karolis1115/Matronix/Pictures/20221025_215015.jpg

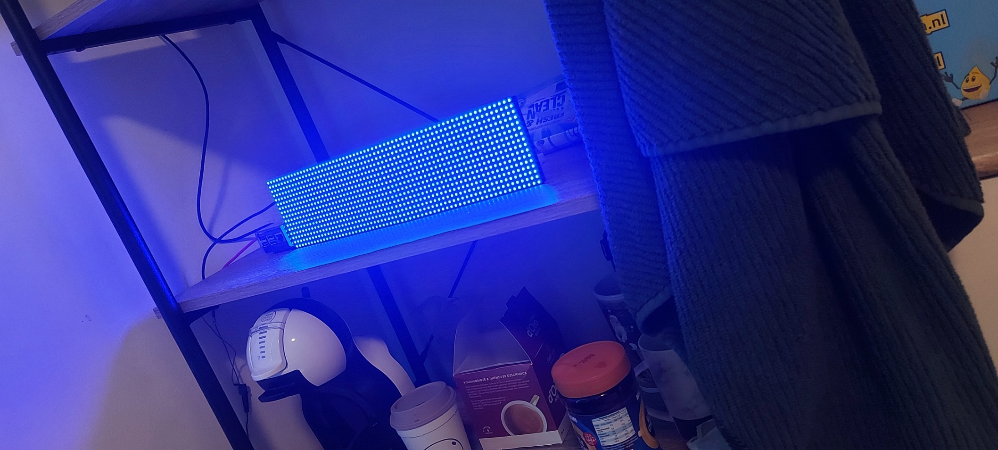
Pictures/20221025_215015.jpg
