karolis1115/Matronix/Pictures/20221025_220137.jpg

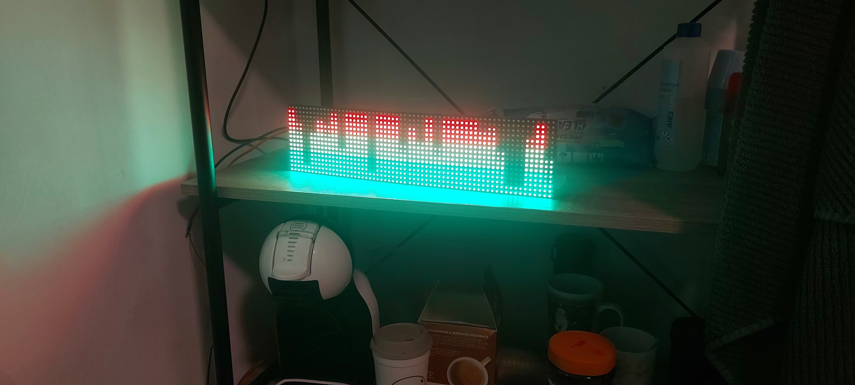
Pictures/20221025_220137.jpg
