karolis1115/Matronix/Pictures/20221025_220200.jpg

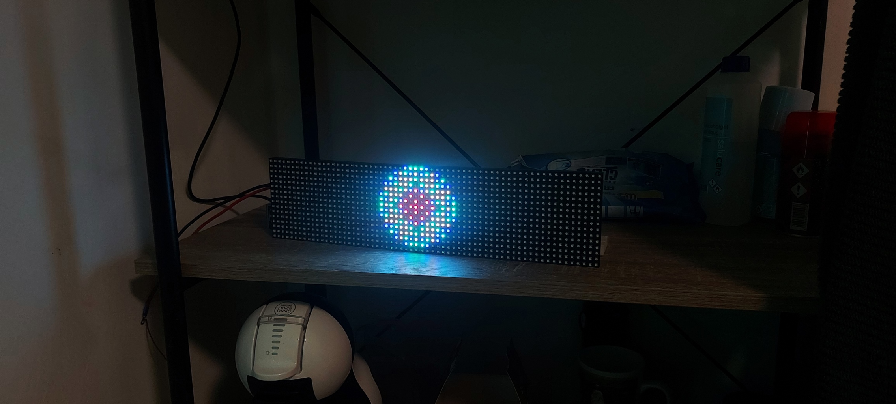
Pictures/20221025_220200.jpg
