karolis1115/Matronix/CAD/PCB assembly with all edge connectors V2/Dimmension_test.3mf

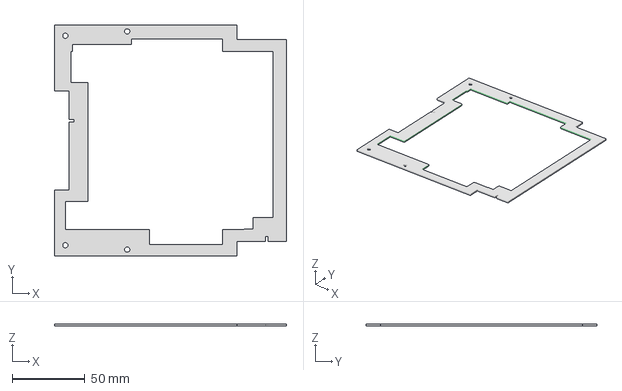
[picture p37: CAD file, 2023-01-07]
CAD/PCB assembly with all edge connectors V2/Dimmension_test.3mf
159.5 x 159.0 x 1.52 mm
