karolis1115/Matronix/CAD/PCB outline with 3 edge connectors and Raspberry pi outline/2x20 Stacking Header.step.SLDPRT

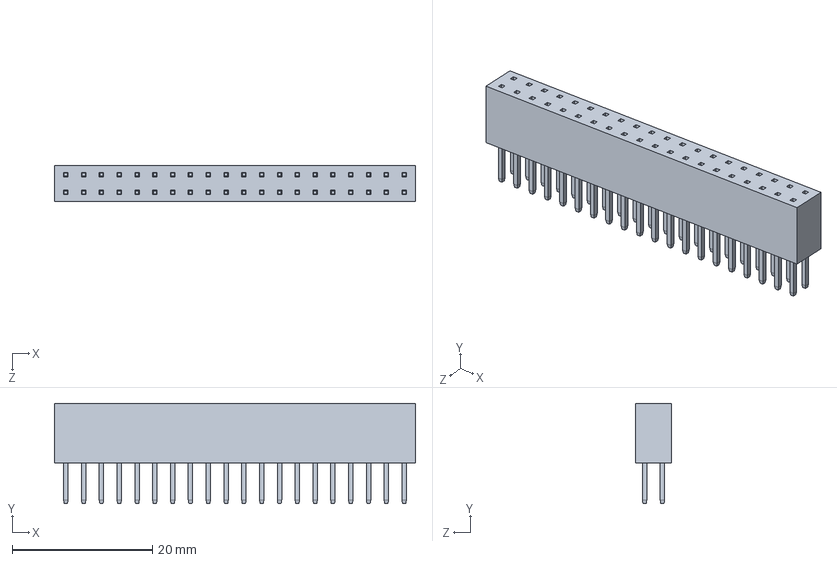
[picture p38: CAD file, 2023-01-07]
CAD/PCB outline with 3 edge connectors and Raspberry pi outline/2x20 Stacking Header.step.SLDPRT
51.5 x 14.3 x 5.08 mm
