karolis1115/Matronix/CAD/PCB outline with 3 edge connectors and Raspberry pi outline/raspberry-pi-4-model-b-1.snapshot.3/Microphone Plug, RPi4ModelB.SLDPRT

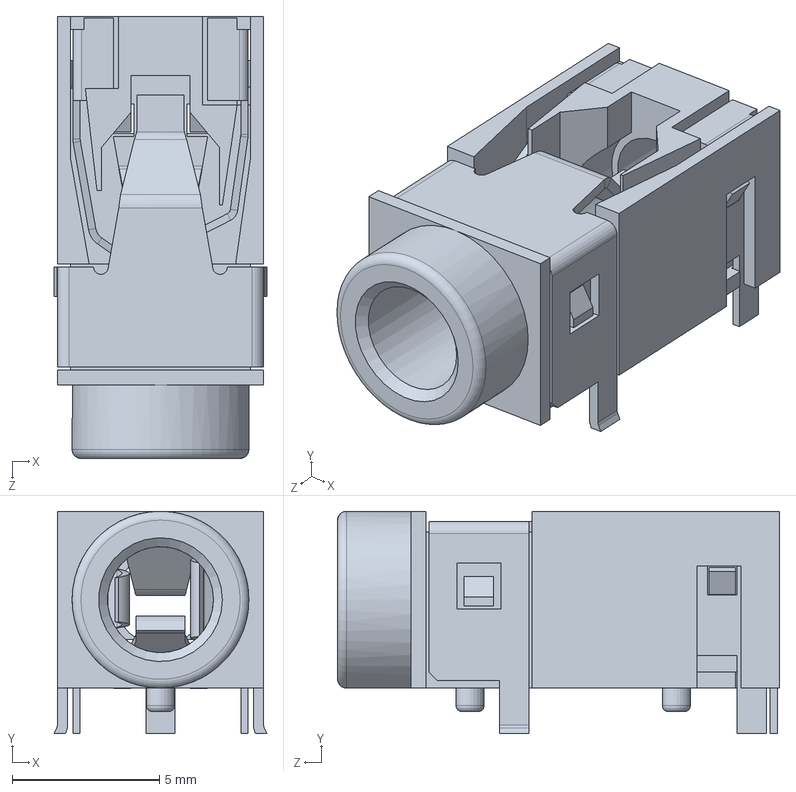
[picture p39: CAD file, 2023-01-07]
CAD/PCB outline with 3 edge connectors and Raspberry pi outline/raspberry-pi-4-model-b-1.snapshot.3/Microphone Plug, RPi4ModelB.SLDPRT
7.23 x 7.55 x 15.0 mm
