karolis1115/Matronix/3D models/LED DISPLAY 32x16 Adafruit.SLDPRT

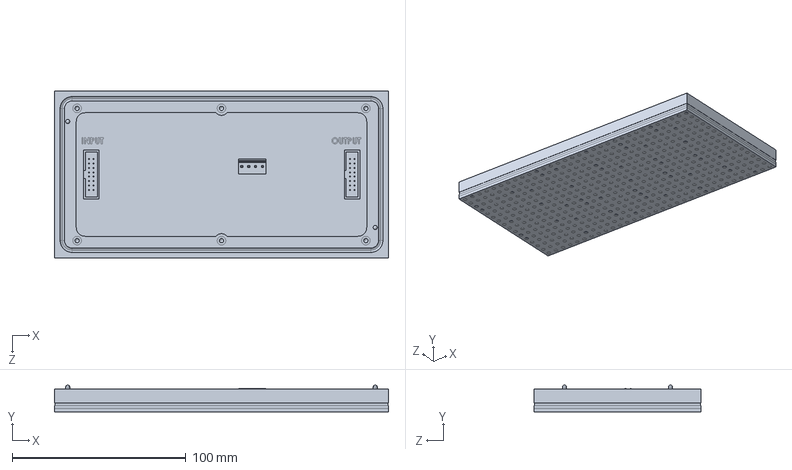
[picture p40: CAD file, 2023-01-07]
3D models/LED DISPLAY 32x16 Adafruit.SLDPRT
192.0 x 15.5 x 96.0 mm
