karolis1115/Matronix/CAD/DIsplay Module PCB.STEP

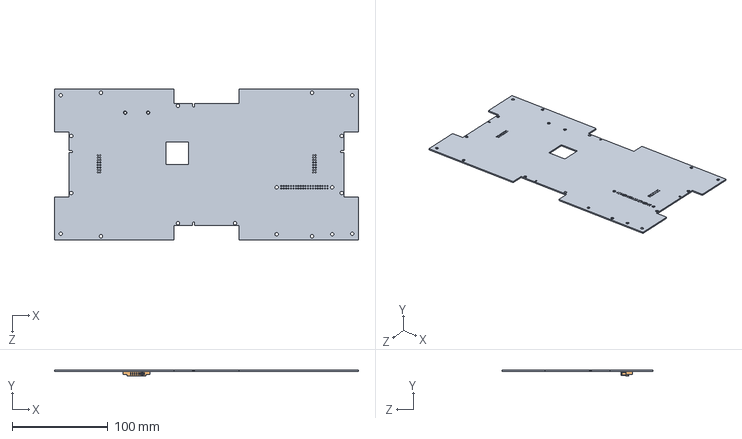
[picture p42: CAD file, 2023-01-21]
CAD/DIsplay Module PCB.STEP
317.5 x 6.37 x 157.5 mm
PCB
