karolis1115/Matronix/CAD/LED Matrix Display Redesign/DIsplay Module PCB.3MF

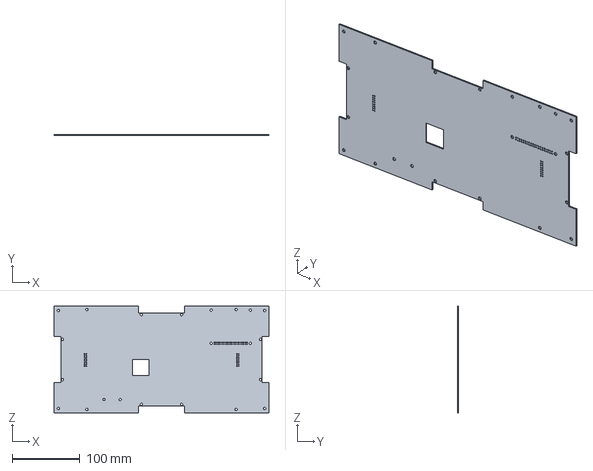
[picture p43: CAD file, 2023-01-07]
CAD/LED Matrix Display Redesign/DIsplay Module PCB.3MF
317.5 x 1.57 x 157.5 mm
