karolis1115/Matronix/CAD/LED Matrix Display Redesign/raspberry-pi-4-model-b-1.snapshot.3/Female Micro HDMI Connector, RPi4ModelB.SLDPRT

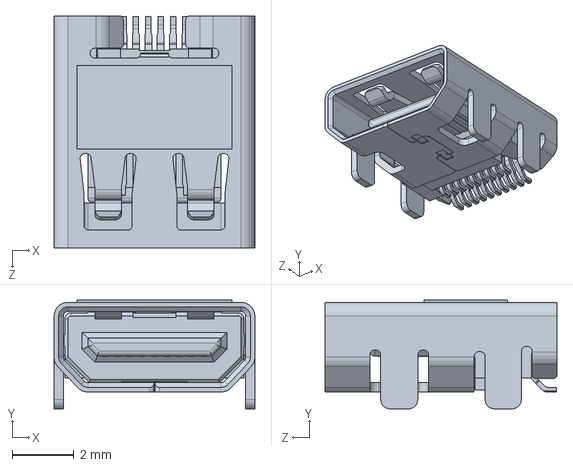
[picture p44: CAD file, 2023-01-07]
CAD/LED Matrix Display Redesign/raspberry-pi-4-model-b-1.snapshot.3/Female Micro HDMI Connector, RPi4ModelB.SLDPRT
6.50 x 3.52 x 7.50 mm
