karolis1115/Matronix/CAD/PCB assembly w Edge connectors/PCB asembly w Edge Connectors V2.3mf

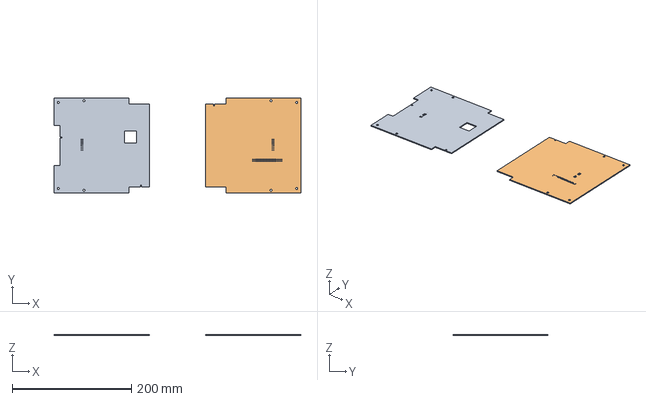
[picture p45: CAD file, 2023-01-07]
CAD/PCB assembly w Edge connectors/PCB asembly w Edge Connectors V2.3mf
413.6 x 159.0 x 1.58 mm
