karolis1115/Matronix/CAD/PCB assembly with all edge connectors V2/Box Header 8x2 16 pin.SLDPRT

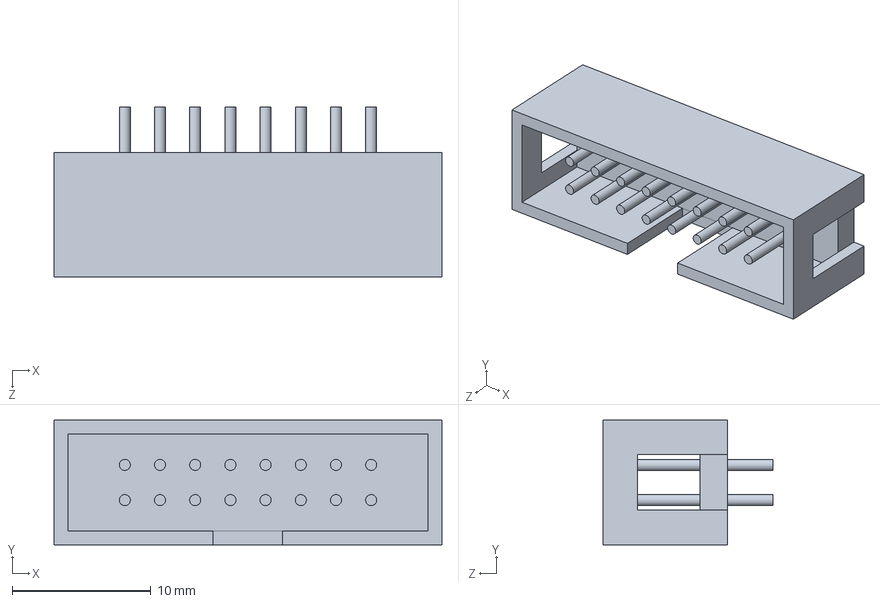
[picture p46: CAD file, 2023-01-07]
CAD/PCB assembly with all edge connectors V2/Box Header 8x2 16 pin.SLDPRT
28.0 x 9.00 x 12.3 mm
