karolis1115/Matronix/CAD/PCB assembly/PCB asembly split.3mf

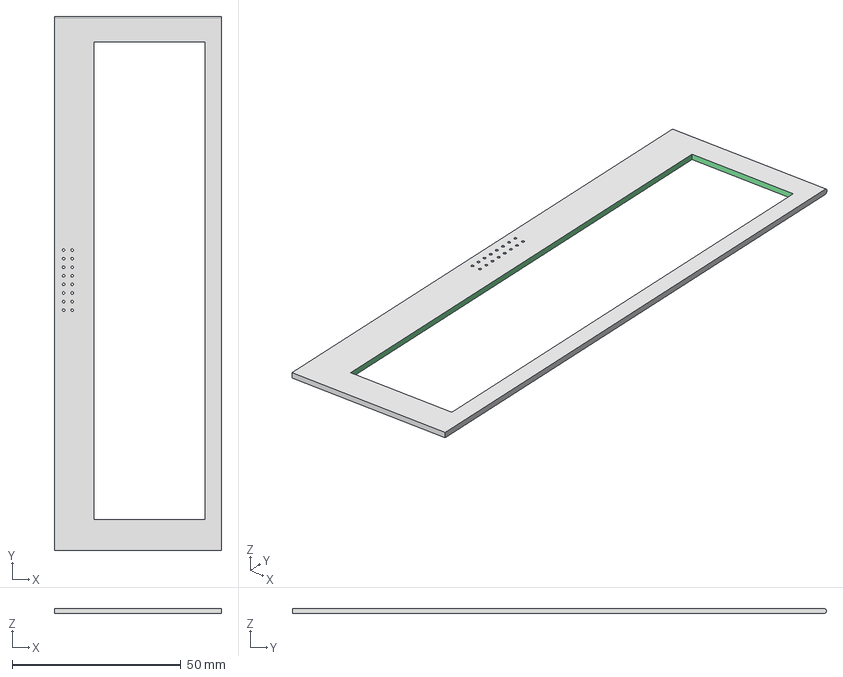
[picture p47: CAD file, 2023-01-07]
CAD/PCB assembly/PCB asembly split.3mf
49.5 x 158.0 x 1.57 mm
