karolis1115/Matronix/CAD/PCB outline with 3 edge connectors and Raspberry pi outline/PCB asembly w Edge Connectors hollowed.3mf

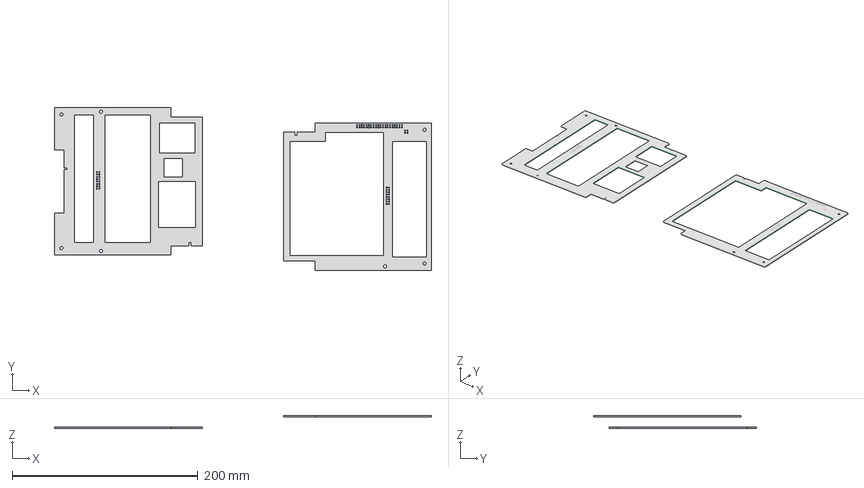
[picture p48: CAD file, 2023-01-07]
CAD/PCB outline with 3 edge connectors and Raspberry pi outline/PCB asembly w Edge Connectors hollowed.3mf
406.1 x 175.5 x 14.0 mm
