karolis1115/Matronix/CAD/PCB outline with 3 edge connectors and Raspberry pi outline/raspberry-pi-4-model-b-1.snapshot.3/MxL7704 Universal PMIC, RPi4ModelB.SLDPRT

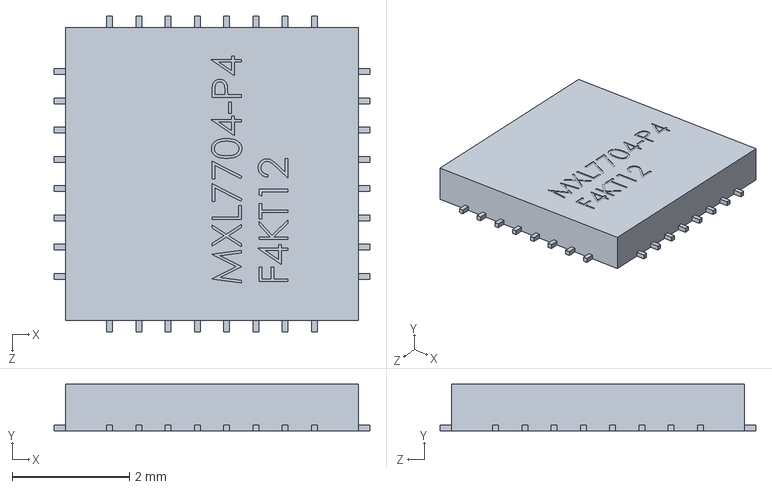
[picture p49: CAD file, 2023-01-07]
CAD/PCB outline with 3 edge connectors and Raspberry pi outline/raspberry-pi-4-model-b-1.snapshot.3/MxL7704 Universal PMIC, RPi4ModelB.SLDPRT
5.40 x 0.8 x 5.40 mm
