karolis1115/Matronix/CAD/LED Matrix Display Redesign/raspberry-pi-4-model-b-1.snapshot.3/Broadcom BCM54213PE Gigabit Ethernet Transceiver, RPi4ModelB.SLDPRT

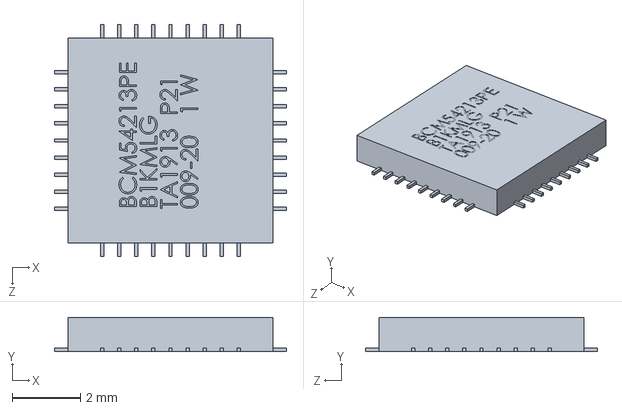
[picture p50: CAD file, 2023-01-07]
CAD/LED Matrix Display Redesign/raspberry-pi-4-model-b-1.snapshot.3/Broadcom BCM54213PE Gigabit Ethernet Transceiver, RPi4ModelB.SLDPRT
6.80 x 1.00 x 6.80 mm
