karolis1115/Matronix/CAD/PCB assembly with all edge connectors V2/PCB asembly w Edge Connectors.DXF

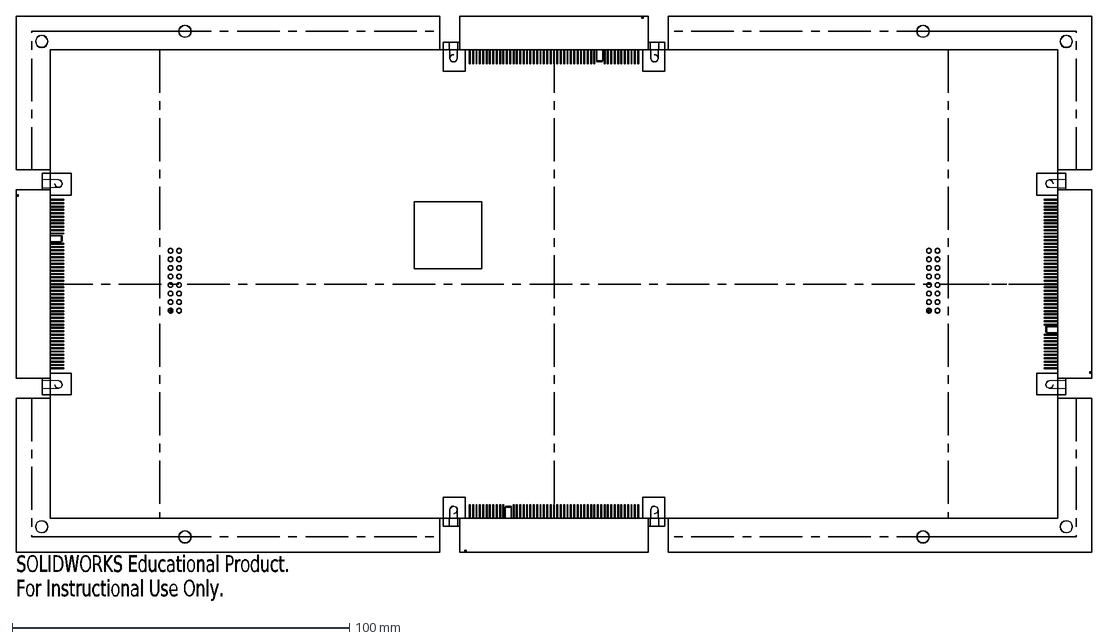
[picture p51: CAD file, 2023-01-07]
CAD/PCB assembly with all edge connectors V2/PCB asembly w Edge Connectors.DXF
SOLIDWORKS Educational Product.
For Instructional Use Only.
