karolis1115/Matronix/CAD/PCB assembly/PCB asemblyV2 split.stl

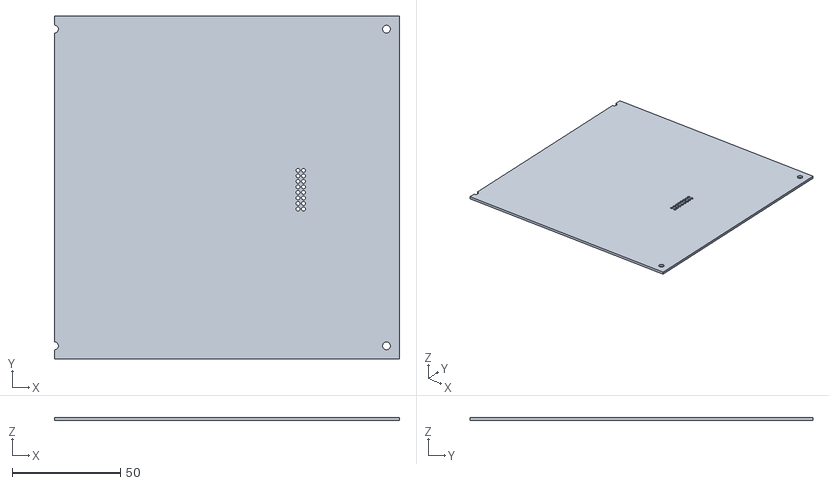
[picture p52: CAD file, 2023-01-07]
CAD/PCB assembly/PCB asemblyV2 split.stl
159.0 x 158.0 x 1.57
