karolis1115/Matronix/CAD/PCB outline with 3 edge connectors and Raspberry pi outline/PCB asembly w Edge Connectors V2.STL

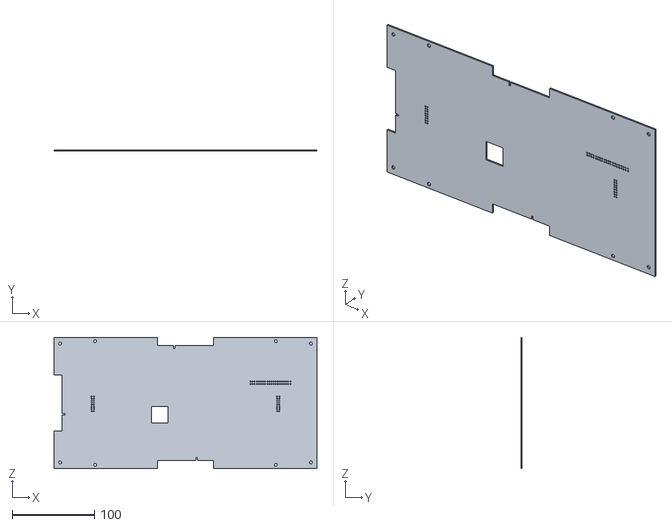
[picture p53: CAD file, 2023-01-07]
CAD/PCB outline with 3 edge connectors and Raspberry pi outline/PCB asembly w Edge Connectors V2.STL
319.0 x 1.57 x 159.0
