karolis1115/Matronix/CAD/PCB outline with 3 edge connectors and Raspberry pi outline/raspberry-pi-4-model-b-1.snapshot.3/2.54 mm DUPONT MALE PIN HEADER, IO, 2X20, RPi4ModelB.SLDPRT

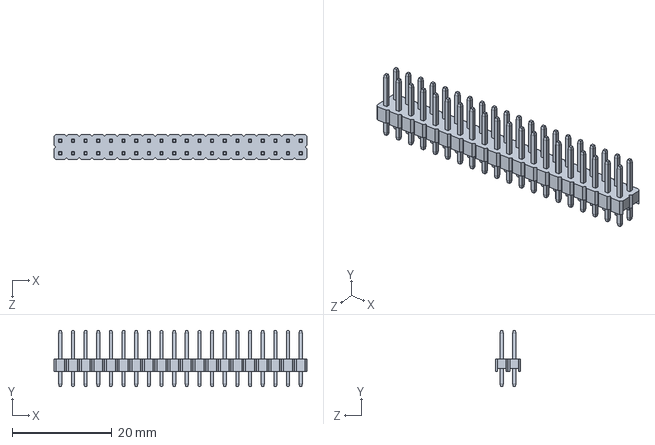
[picture p54: CAD file, 2023-01-07]
CAD/PCB outline with 3 edge connectors and Raspberry pi outline/raspberry-pi-4-model-b-1.snapshot.3/2.54 mm DUPONT MALE PIN HEADER, IO, 2X20, RPi4ModelB.SLDPRT
50.8 x 11.3 x 5.08 mm
