karolis1115/Matronix/CAD/LED Matrix Display Redesign/raspberry-pi-4-model-b-1.snapshot.3/Camera Connector, RPi4ModelB.SLDPRT

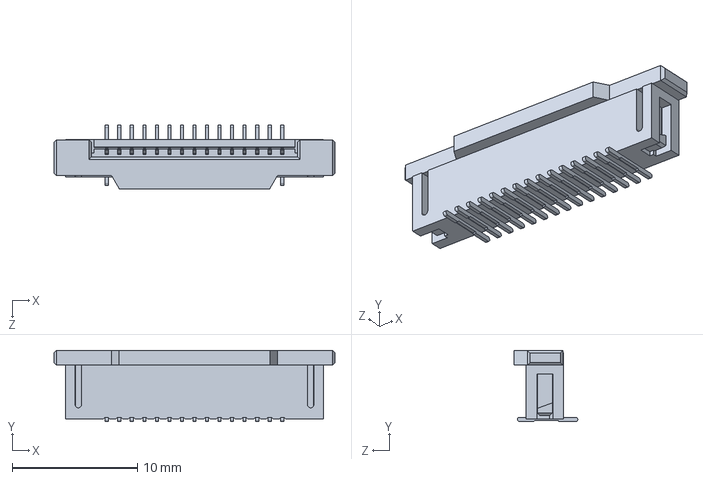
[picture p55: CAD file, 2023-01-07]
CAD/LED Matrix Display Redesign/raspberry-pi-4-model-b-1.snapshot.3/Camera Connector, RPi4ModelB.SLDPRT
22.4 x 5.68 x 5.07 mm
