karolis1115/Matronix/CAD/PCB assembly/PCB asembly V3_Gutted.3mf

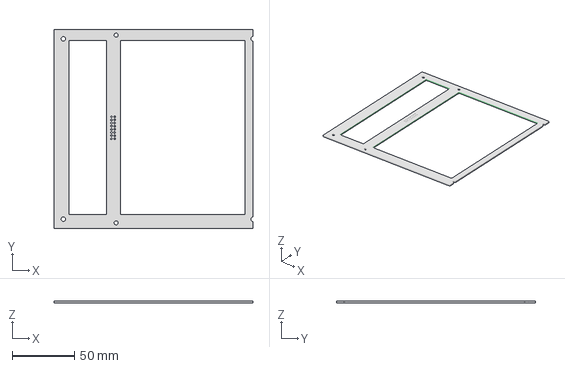
[picture p56: CAD file, 2023-01-07]
CAD/PCB assembly/PCB asembly V3_Gutted.3mf
160.0 x 160.0 x 1.57 mm
