karolis1115/Matronix/3D models/raspberry-pi-4-model-b-1.snapshot.3/2X USB3.0 PORTS, RPi4ModelB.SLDPRT

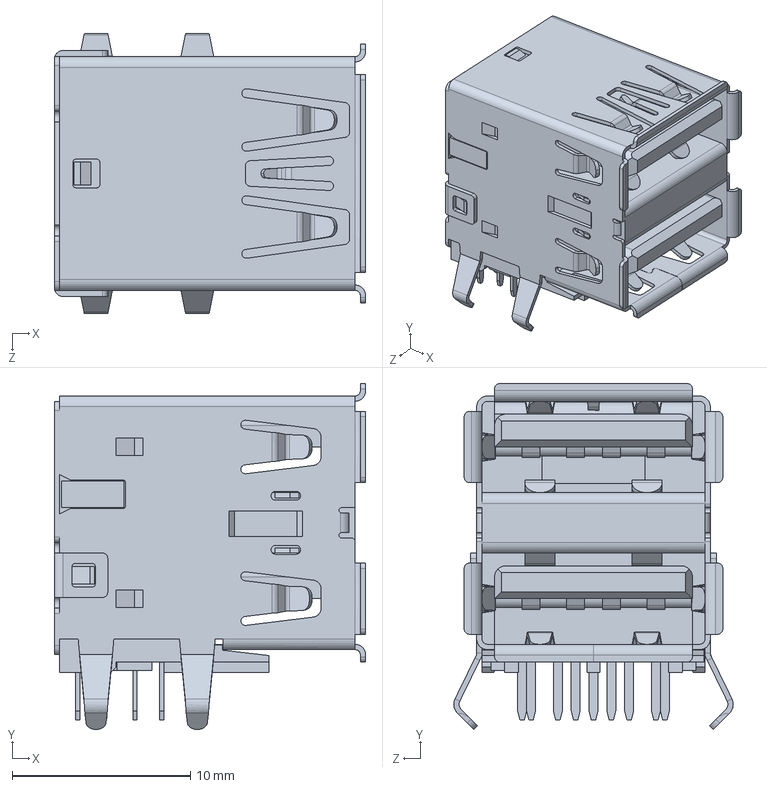
[picture p57: CAD file, 2023-01-07]
3D models/raspberry-pi-4-model-b-1.snapshot.3/2X USB3.0 PORTS, RPi4ModelB.SLDPRT
17.5 x 19.4 x 15.7 mm
