karolis1115/Matronix/CAD/LED Matrix Display Redesign/40 Pin Long Female header.SLDPRT

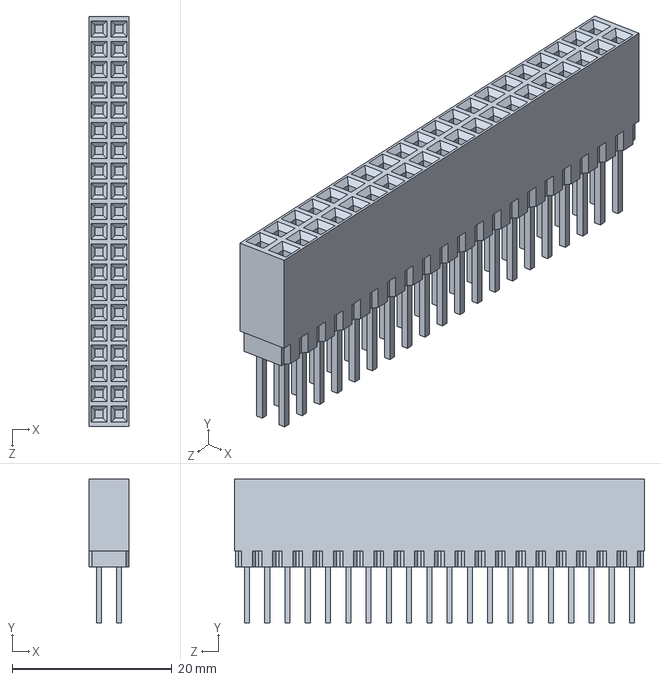
[picture p58: CAD file, 2023-01-07]
CAD/LED Matrix Display Redesign/40 Pin Long Female header.SLDPRT
5.00 x 18.0 x 51.4 mm
