karolis1115/Matronix/CAD/PCB assembly w Edge connectors/PCB asembly Connector allignment.DXF

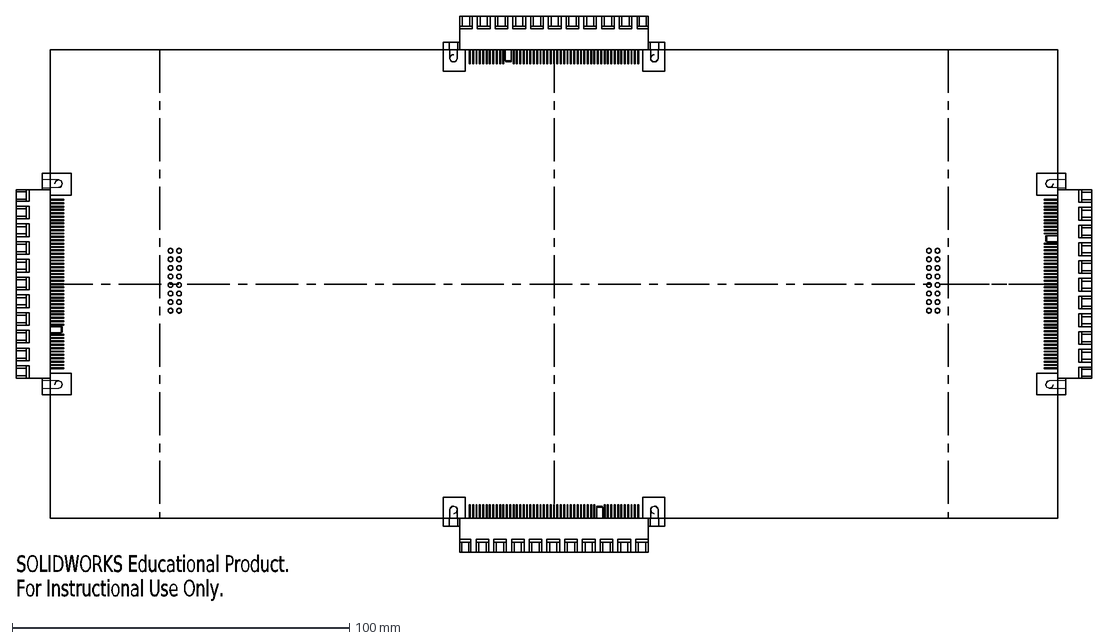
[picture p59: CAD file, 2023-01-07]
CAD/PCB assembly w Edge connectors/PCB asembly Connector allignment.DXF
SOLIDWORKS Educational Product.
For Instructional Use Only.
