karolis1115/Matronix/CAD/PCB assembly/PCB asembly+DimpleHoles_SPlit+Guttedmf.3mf

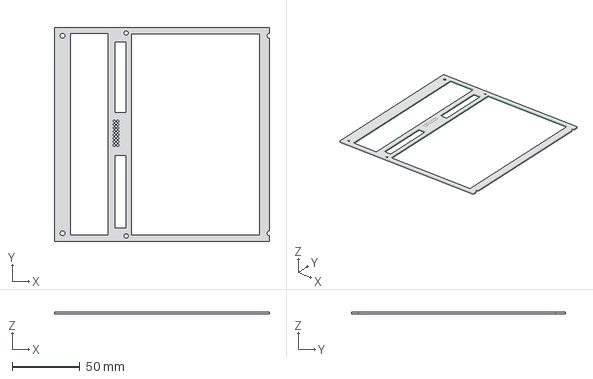
[picture p60: CAD file, 2023-01-07]
CAD/PCB assembly/PCB asembly+DimpleHoles_SPlit+Guttedmf.3mf
159.0 x 158.0 x 1.57 mm
