karolis1115/Matronix/CAD/PCB outline with 3 edge connectors and Raspberry pi outline/female_header_a-bl254-eg-g02d.stp.SLDPRT

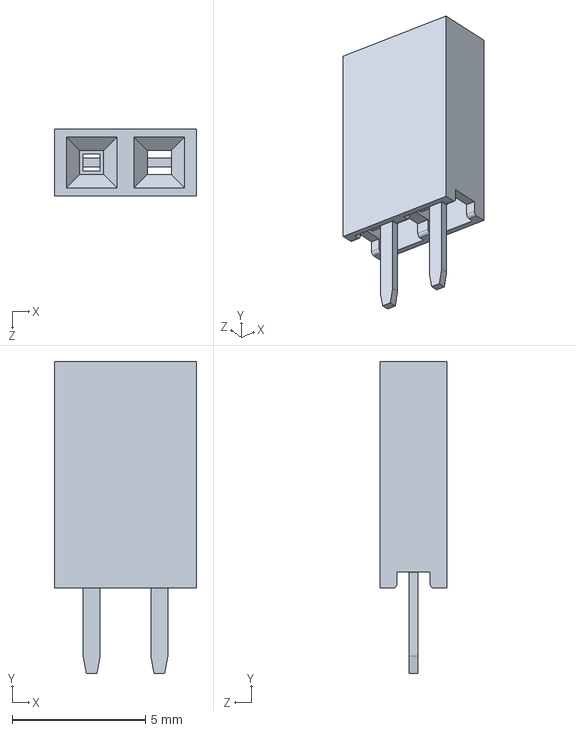
[picture p61: CAD file, 2023-01-07]
CAD/PCB outline with 3 edge connectors and Raspberry pi outline/female_header_a-bl254-eg-g02d.stp.SLDPRT
5.33 x 11.7 x 2.50 mm
