karolis1115/Matronix/CAD/PCB outline with 3 edge connectors and Raspberry pi outline/raspberry-pi-4-model-b-1.snapshot.3/VIA VL805 PCIe USB 3.0 controller, RPi4ModelB.SLDPRT

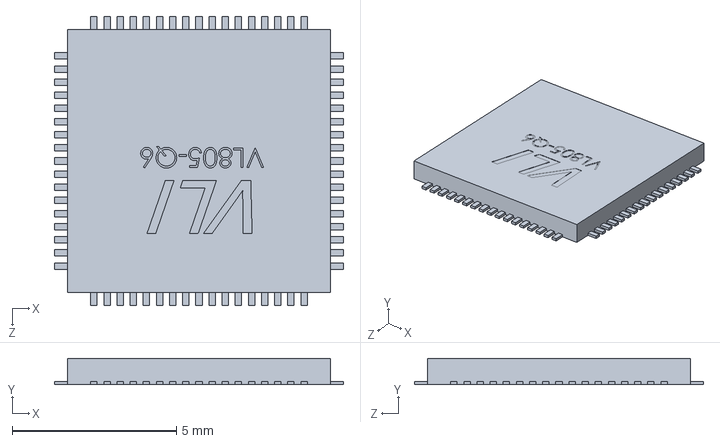
[picture p62: CAD file, 2023-01-07]
CAD/PCB outline with 3 edge connectors and Raspberry pi outline/raspberry-pi-4-model-b-1.snapshot.3/VIA VL805 PCIe USB 3.0 controller, RPi4ModelB.SLDPRT
8.80 x 0.8 x 8.80 mm
