karolis1115/Matronix/3D models/raspberry-pi-4-model-b-1.snapshot.3/Cypress CYW43455 Wireless Module Cover, RPi4ModelB.SLDPRT

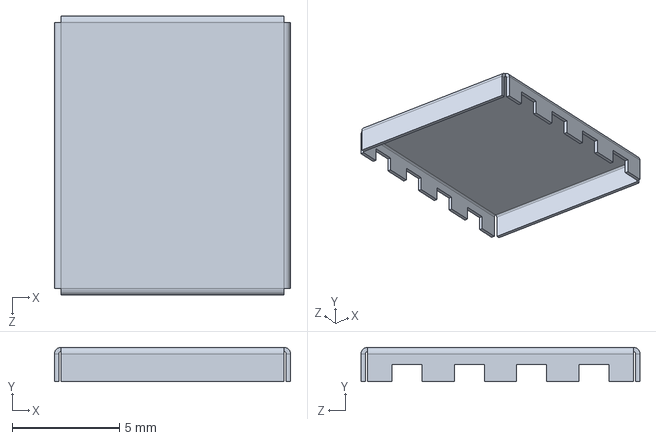
[picture p63: CAD file, 2023-01-07]
3D models/raspberry-pi-4-model-b-1.snapshot.3/Cypress CYW43455 Wireless Module Cover, RPi4ModelB.SLDPRT
11.0 x 1.60 x 13.0 mm
