karolis1115/Matronix/CAD/LED Matrix Display Redesign/DIsplay Module PCB split.3mf

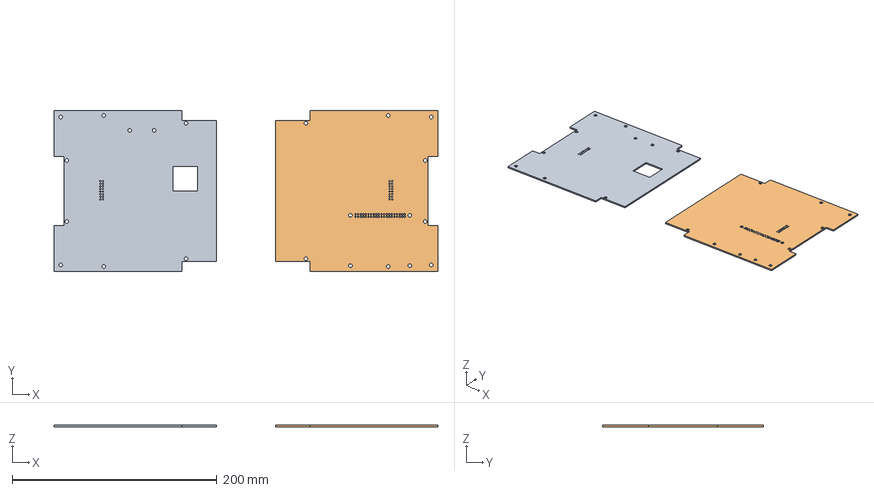
[picture p64: CAD file, 2023-01-07]
CAD/LED Matrix Display Redesign/DIsplay Module PCB split.3mf
375.0 x 157.5 x 1.57 mm
