karolis1115/Matronix/CAD/PCB assembly w Edge connectors/PCB asembly w Edge ConnectorsV3 (fixed edge connector rotation).DXF

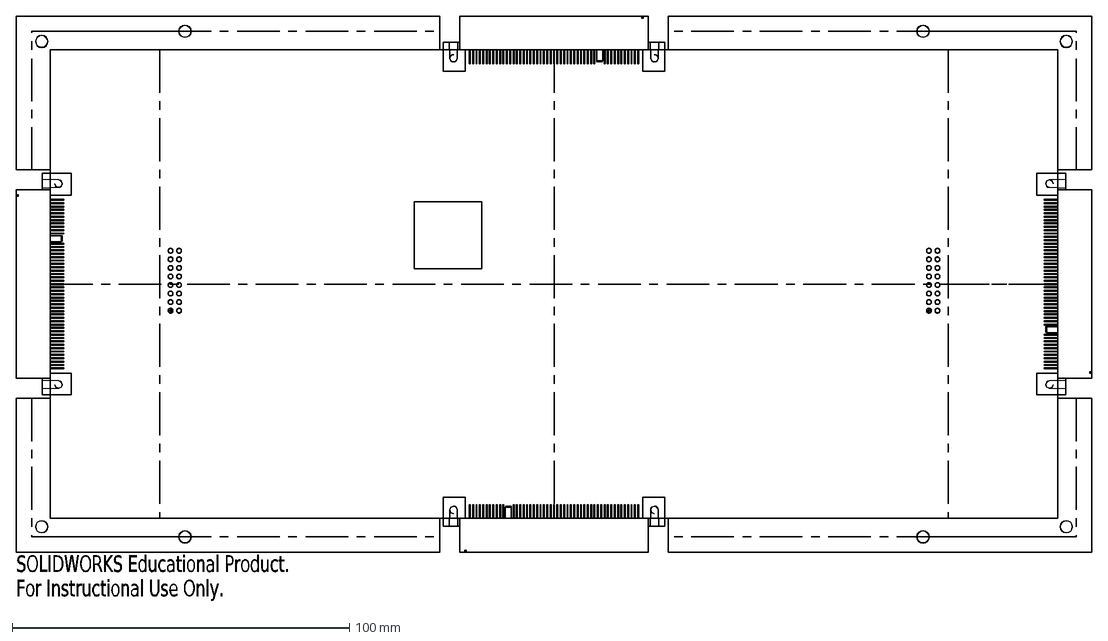
[picture p65: CAD file, 2023-01-07]
CAD/PCB assembly w Edge connectors/PCB asembly w Edge ConnectorsV3 (fixed edge connector rotation).DXF
SOLIDWORKS Educational Product.
For Instructional Use Only.
