karolis1115/Matronix/CAD/LED Matrix Display Redesign/raspberry-pi-4-model-b-1.snapshot.3/PCB, RPi4ModelB.SLDPRT

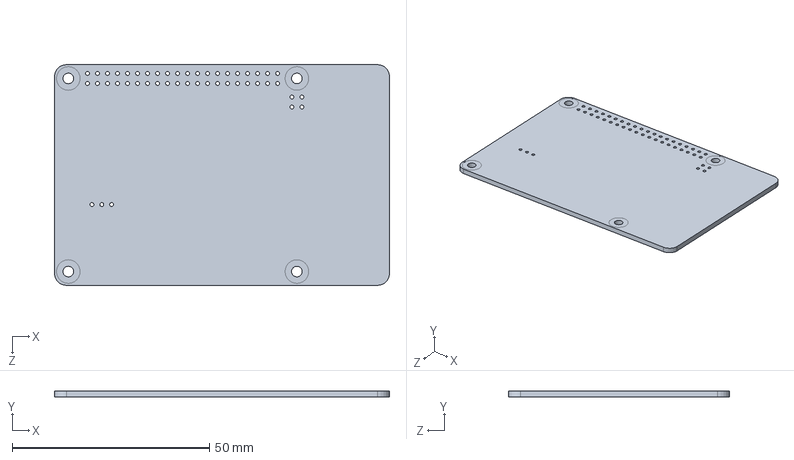
[picture p66: CAD file, 2023-01-07]
CAD/LED Matrix Display Redesign/raspberry-pi-4-model-b-1.snapshot.3/PCB, RPi4ModelB.SLDPRT
85.0 x 1.60 x 56.0 mm
