karolis1115/Matronix/CAD/PCB assembly/PCB asemblyV2 split&hollowed.3mf

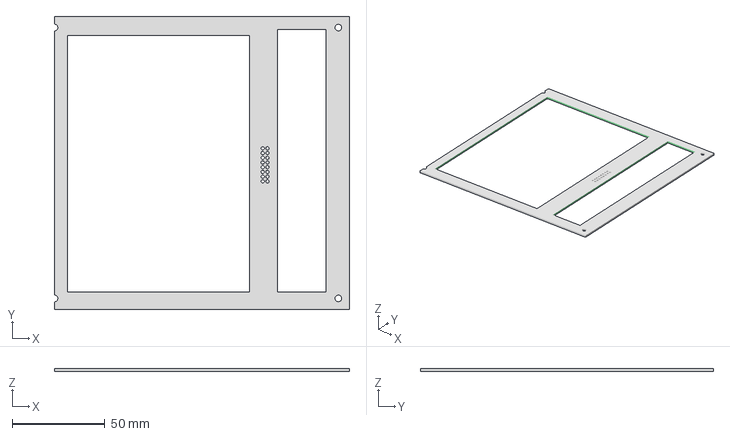
[picture p67: CAD file, 2023-01-07]
CAD/PCB assembly/PCB asemblyV2 split&hollowed.3mf
159.0 x 158.0 x 1.57 mm
