karolis1115/Matronix/CAD/PCB outline with 3 edge connectors and Raspberry pi outline/raspberry-pi-4-model-b-1.snapshot.3/Gigabit Ethernet Port, RPi4ModelB.SLDPRT

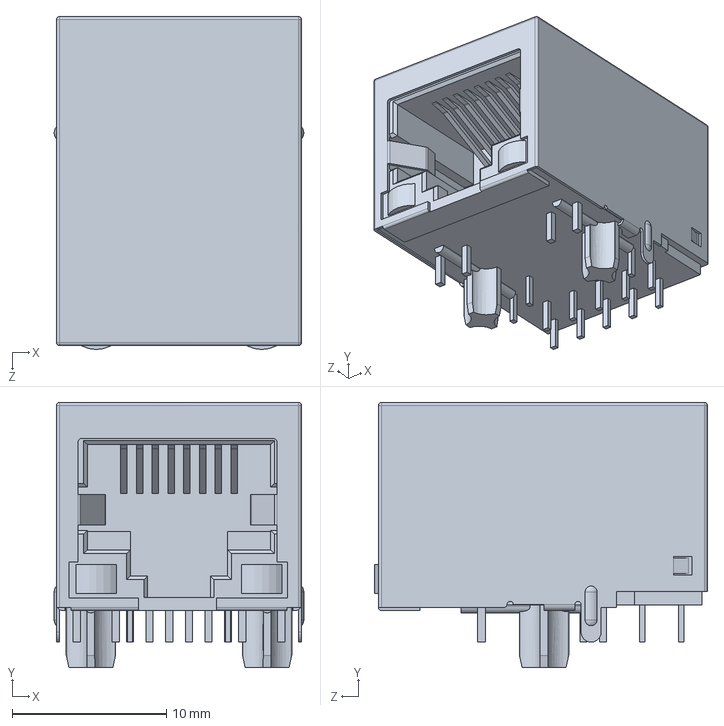
[picture p68: CAD file, 2023-01-07]
CAD/PCB outline with 3 edge connectors and Raspberry pi outline/raspberry-pi-4-model-b-1.snapshot.3/Gigabit Ethernet Port, RPi4ModelB.SLDPRT
16.2 x 17.2 x 21.6 mm
