karolis1115/Matronix/CAD/PCB assembly w Edge connectors/PCB asembly w Edge Connectors V3 .STL

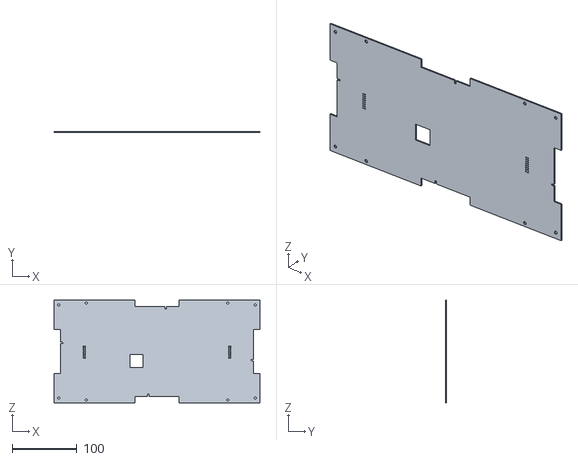
[picture p69: CAD file, 2023-01-07]
CAD/PCB assembly w Edge connectors/PCB asembly w Edge Connectors V3 .STL
319.0 x 1.57 x 159.0
