karolis1115/Matronix/CAD/LED Matrix Display Redesign/raspberry-pi-4-model-b-1.snapshot.3/Broadcom BCM2711B0 CPU, RPi4ModelB.SLDPRT

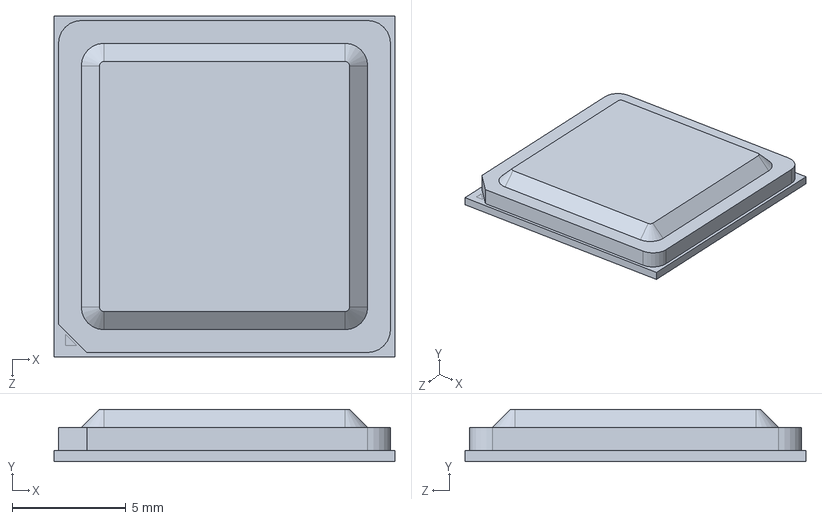
[picture p71: CAD file, 2023-01-07]
CAD/LED Matrix Display Redesign/raspberry-pi-4-model-b-1.snapshot.3/Broadcom BCM2711B0 CPU, RPi4ModelB.SLDPRT
15.0 x 2.30 x 15.0 mm
