karolis1115/Matronix/CAD/PCB outline with 3 edge connectors and Raspberry pi outline/PCB asembly w Edge Connectors.DXF

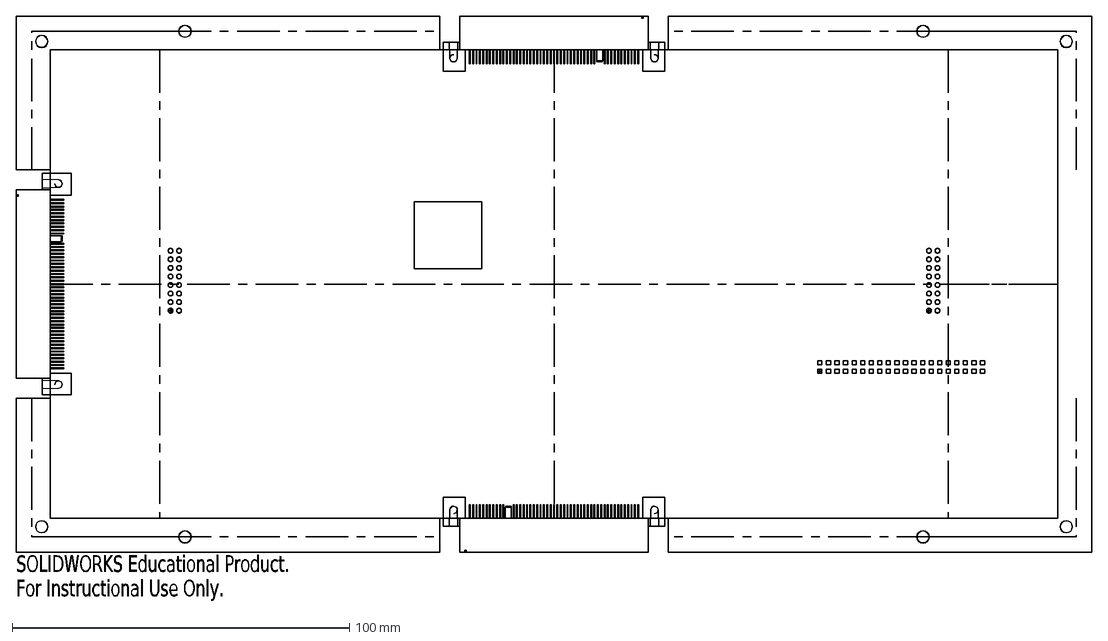
[picture p72: CAD file, 2023-01-07]
CAD/PCB outline with 3 edge connectors and Raspberry pi outline/PCB asembly w Edge Connectors.DXF
SOLIDWORKS Educational Product.
For Instructional Use Only.
