karolis1115/Matronix/CAD/PCB assembly w Edge connectors/Power Cutout.DXF

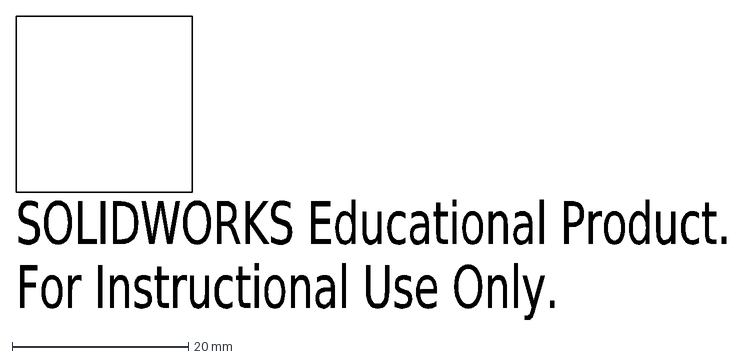
[picture p73: CAD file, 2023-01-07]
CAD/PCB assembly w Edge connectors/Power Cutout.DXF
SOLIDWORKS Educational Product.
For Instructional Use Only.
