karolis1115/Matronix/CAD/PCB outline with 3 edge connectors and Raspberry pi outline/PCB asembly w Edge Connectors V2 gutted rpi header side.3mf

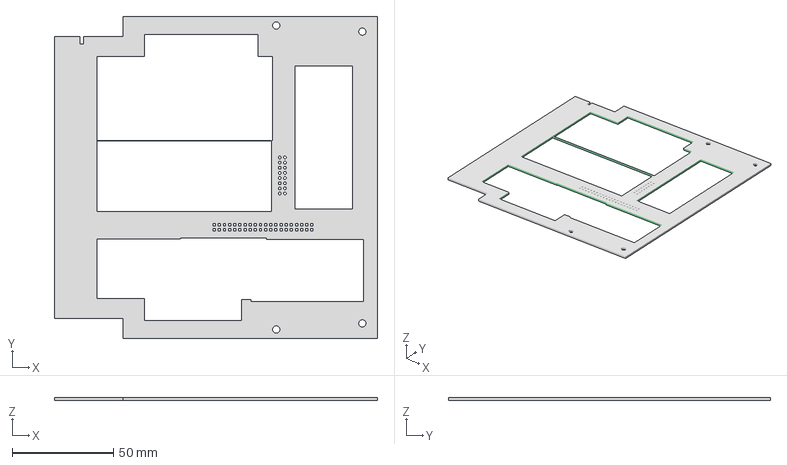
[picture p74: CAD file, 2023-01-07]
CAD/PCB outline with 3 edge connectors and Raspberry pi outline/PCB asembly w Edge Connectors V2 gutted rpi header side.3mf
159.5 x 159.0 x 1.52 mm
