karolis1115/Matronix/CAD/PCB assembly w Edge connectors/Header 8x2 vert 0.1 inch pitch thru.step

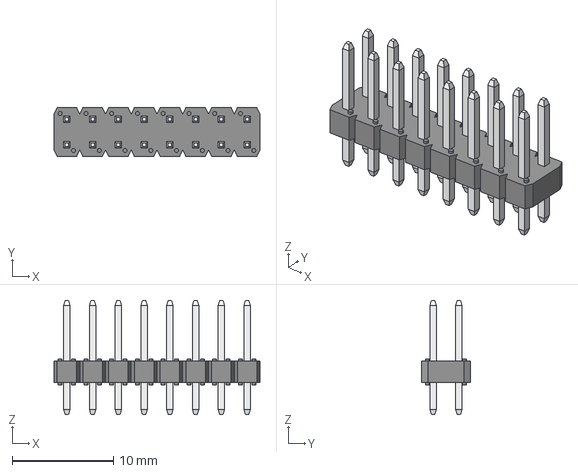
[picture p75: CAD file, 2023-01-07]
CAD/PCB assembly w Edge connectors/Header 8x2 vert 0.1 inch pitch thru.step
20.3 x 4.82 x 11.2 mm
