karolis1115/Matronix/CAD/PCB assembly w Edge connectors/Card edge connector - G630H9812248EU--3DModel-STEP-56544.step-5.STL

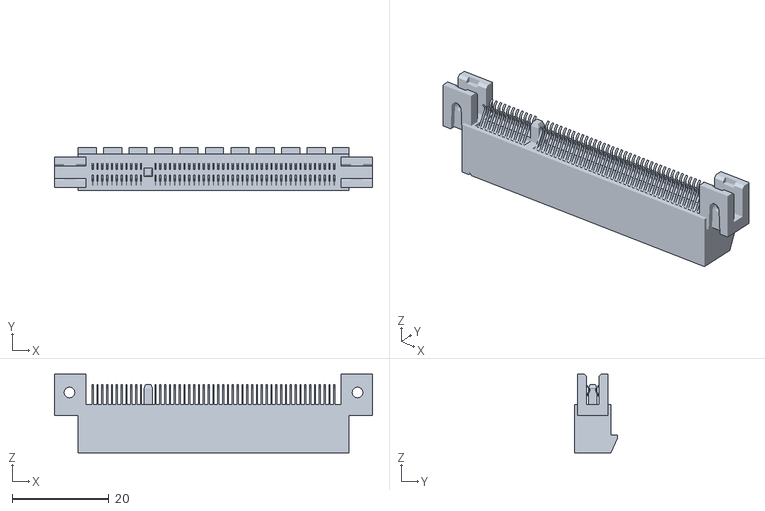
[picture p76: CAD file, 2023-01-07]
CAD/PCB assembly w Edge connectors/Card edge connector - G630H9812248EU--3DModel-STEP-56544.step-5.STL
65.8 x 8.85 x 16.3
