karolis1115/Matronix/CAD/PCB outline with 3 edge connectors and Raspberry pi outline/PCB asembly w Edge Connectors V3 GUTTED.3mf

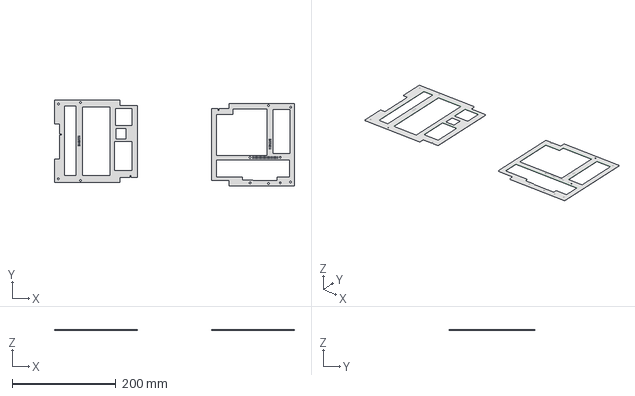
[picture p77: CAD file, 2023-01-07]
CAD/PCB outline with 3 edge connectors and Raspberry pi outline/PCB asembly w Edge Connectors V3 GUTTED.3mf
461.7 x 165.1 x 1.57 mm
