karolis1115/Matronix/CAD/PCB assembly w Edge connectors/PCB asembly Board outline.DXF

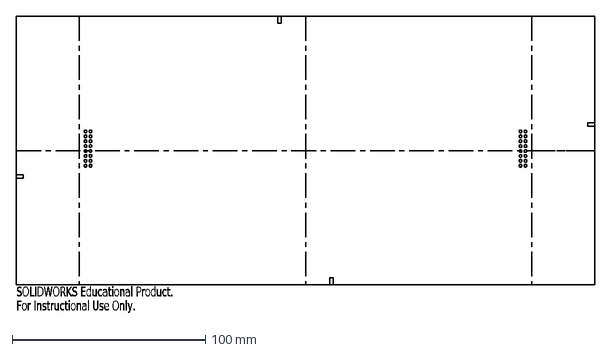
[picture p78: CAD file, 2023-01-07]
CAD/PCB assembly w Edge connectors/PCB asembly Board outline.DXF
SOLIDWORKS Educational Product.
For Instructional Use Only.
