karolis1115/Matronix/CAD/LED Matrix Display Redesign/raspberry-pi-4-model-b-1.snapshot.3/SD Card Slot, RPi4ModelB.SLDPRT

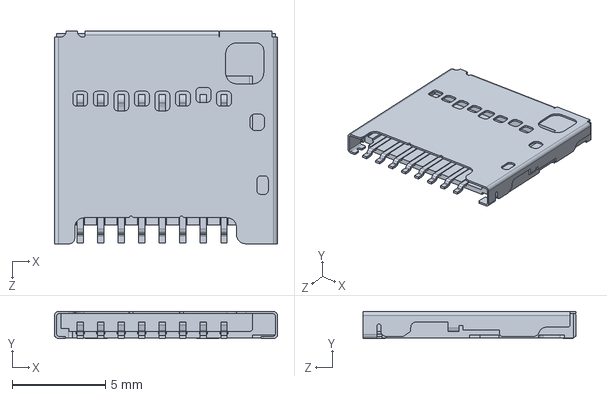
[picture p79: CAD file, 2023-01-07]
CAD/LED Matrix Display Redesign/raspberry-pi-4-model-b-1.snapshot.3/SD Card Slot, RPi4ModelB.SLDPRT
11.9 x 1.45 x 11.4 mm
